TinyCircuits/TinyCircuits-TinyShield-Servo-Driver-ASD2303/images/ASD2303-R-Tutorial-Image-01.jpg

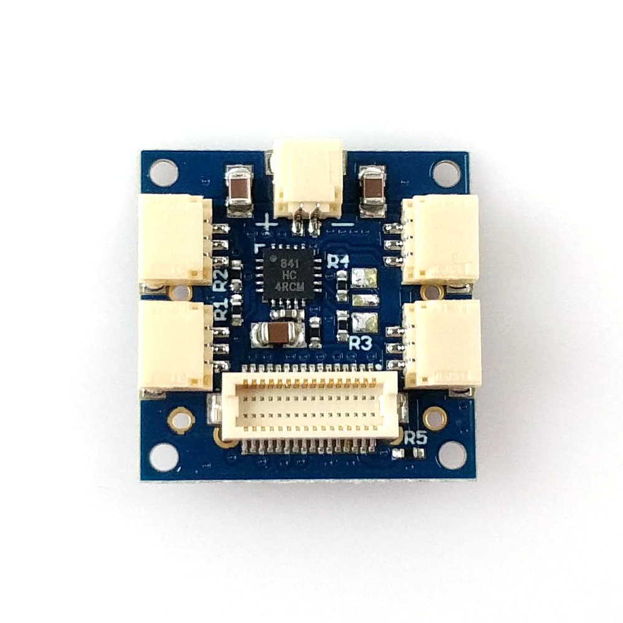
images/ASD2303-R-Tutorial-Image-01.jpg
