TinyCircuits/TinyCircuits-TinyShield-Servo-Driver-ASD2303/images/ASD2303-Tutorial-Image-02.png

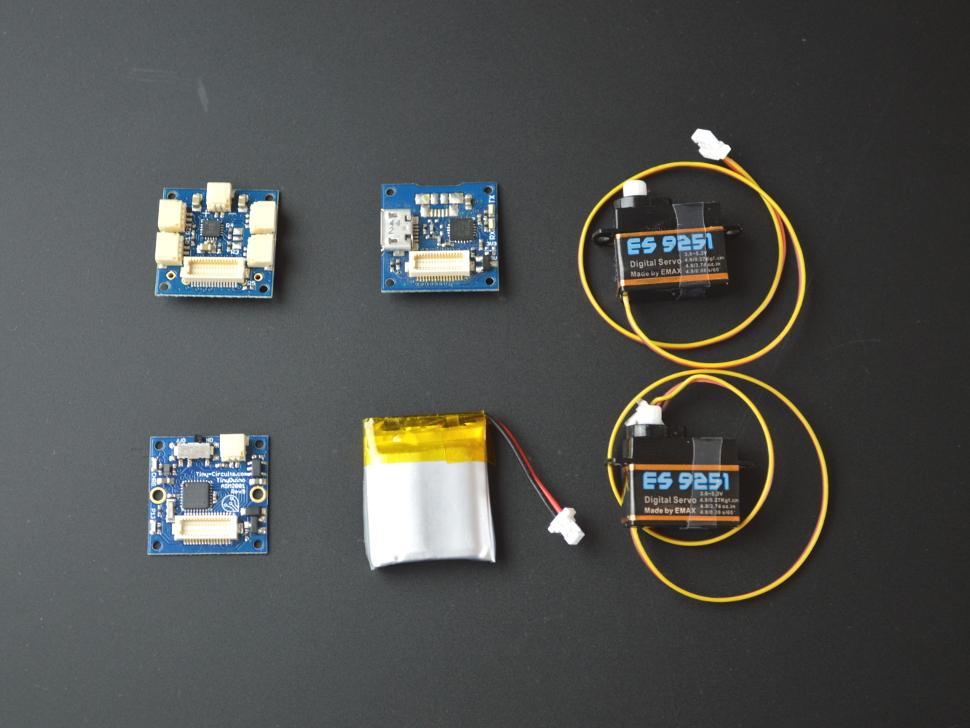
images/ASD2303-Tutorial-Image-02.png
