TinyCircuits/TinyCircuits-TinyShield-Servo-Driver-ASD2303/images/ASD2303-Tutorial-Image-04.png

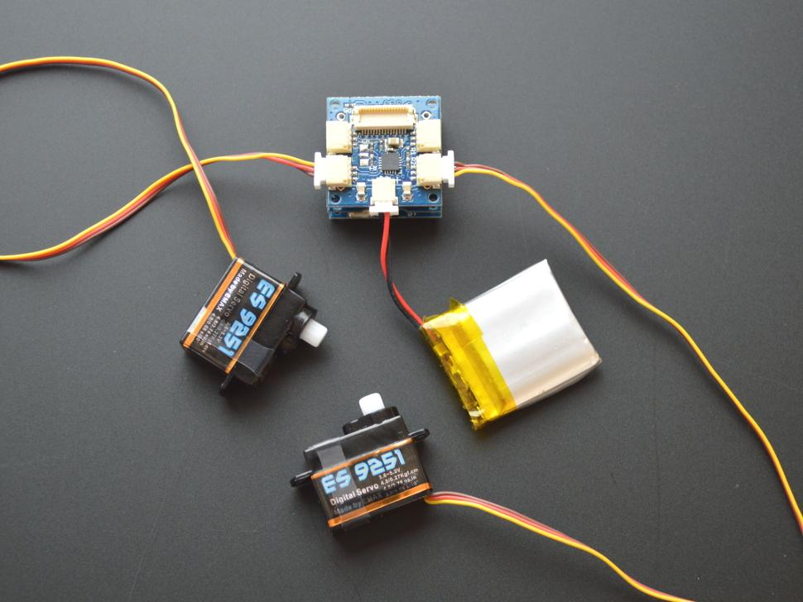
images/ASD2303-Tutorial-Image-04.png
